robotman2412/PX16/tests/highleveltest.asm

// region text
	// IRQ vector.
	.db irqv
	// NMI vector.
	.db nmiv
	// Entry vector.
	.db entry



	// IRQ Handler.
irqv:
	// Update timer status.
	MOV [PC~timerstatus], 1
	
	// Acknowledge timer.
	MOV [0xfffe], 0x0400
	
	MOV PF, [ST]
	MOV PC, [ST]



	// NMI Handler.
nmiv:
	MOV PF, [ST]
	MOV PC, [ST]



	// Code entrypoint.
entry:
	// Generic initialiser.
	MOV ST, 0xffff
	SUB ST, [0xffff]
	OR  PF, 0x0003
	
	// Show sumthin.
	LEA R1, [PC~img_logo0]
	LEA R2, [PC~img_logo]
.loop:
	MOV R0, R1
	LEA.JSR PC, [PC~disp_img]
	LEA.JSR PC, [PC~waittimer]
	ADD R1, 32
	CMP R1, R2
	LEA.ULE PC, [PC~.loop]
	
	// Ded.
	DEC PC



	// Waits using the timers.
waittimer: // region
	MOV [ST], R0
	
	// Set timer waiting device.
	MOV [PC~timerstatus], 0
	
	// Set timer value.
	MOV R0, 0xffff
	MOV [0xfffa], R0
	MOV [0xfffb], R0
	// Set timer limit.
	MOV [0xfff8], 0xa120
	MOV [0xfff9], 0x0007
	// Start timer.
	MOV [0xfffe], 0x0505
	
	// Enable interrupts.
	OR  PF, 0x0002
	
	// Wait until timerstatus is nonzero.
.loop:
	CMP1 [PC~timerstatus]
	LEA.ULT PC, [PC~.loop]
	
	// Return.
	MOV PC, [ST]
	// endregion



	// Waits for a bit.
waitloop: // region
	MOV [ST], R0
	MOV R0, 0x1000
.loop:
	DEC R0
	LEA.CS PC, [PC~.loop]
	MOV R0, [ST]
	MOV PC, [ST]
	// endregion



	// Simple helper that copies source to the screen.
	// Parameters: src.
disp_img: // region
	// Function entry.
	MOV [ST], R2
	MOV [ST], R1
	
	// Subroutine call: memcpy(0xffc0, src, 32)
	// Set limit to 32 (the size of the screen).
	MOV R2, 32
	// Move over the source to the proper register.
	MOV R1, R0
	// Set dest to 0xffc0 (the address of the screen).
	MOV R0, 0xffc0
	// Jump to subroutine.
	LEA.JSR PC, [PC~memcpy]
	
	// Return.
	MOV R1, [ST]
	MOV R2, [ST]
	MOV PC, [ST]
	// endregion



	// Copies a region of memory to another.
	// Does not check for overlapping memory.
	// Parameters: dst, src, size.
memcpy: // region
	// Function entry.
	MOV [ST], R3
	
	// Limit prep and check size > 0.
	DEC R2
	LEA.ULT PC, [PC~.exit]
	
	// Copying loop.
.loop:
	// Loads from the source.
	MOV R3, [R1+R2]
	// Stores to the destination.
	MOV [R0+R2], R3
	// Decrements the limit.
	DEC R2
	// Loop condition.
	LEA.UGE PC, [PC~.loop]
	
	// Return.
.exit:
	MOV R3, [ST]
	MOV PC, [ST]
	// endregion


//endregion text.



// region rodata
	.section ".rodata"

img_logo0:
	// region
	//    0 ' ' ' ' ' ' ' ' ' ' ' ' ' ' ' ' ' ' ' ' ' ' ' ' ' ' ' ' ' ' 31
	//  0 . . . . . . . . . . . . . . . . . . . . . . . . . . . . . . . .
	//  1 . . . . . . . . . . . . . . . . . . . . . . . . . . . . . . . .
	//  2 . . . . . . . . . . . . . . . . . . . . . . . . . . . . . . . .
	//  3 . . . . . . . . . . . . . . . . . . . . . . . . . . . . . . . .
	//  4 . . . . . . . . . . . . . . . . . . . . . . . . . . . . . . . .
	//  5 . . . . . . . . . . . . . . . . . . . . . . . . . . . . . . . .
	//  6 . . . . . . . . . . . . . . . . . . . . . . . . . . . . . . . .
	//  7 . . . . . . . . . . . . . . . . . . . . . . . . . . . . . . . .
	//  8 . . . . . . . . . . . . . . . . . . . . . . . . . . . . . . . .
	//  9 . . . . . . . . . . . . . . . . . . . . . . . . . . . . . . . .
	// 10 . . . . . . . . . . . . . . . . . . . . . . . . . . . . . . . .
	// 11 . . . . . . . . . . . . . . . . . . . . . . . . . . . . . . . .
	// 12 . @ . . . . . . . . . @ . . . . . . . . . . . . . . . . . . . .
	// 13 . @ . . . . . @ . @ . @ . . . . . @ . @ . . . @ @ . . . . . . .
	// 14 . . . . . . . . . . . . . . . . . . . . . . . . . . . . . . . .
	// 15 . . . . . . . . . . . . . . . . . . . . . . . . . . . . . . . .
	.db 0x0000
	.db 0x3000
	.db 0x0000
	.db 0x0000
	.db 0x0000
	.db 0x0000
	.db 0x0000
	.db 0x2000
	.db 0x0000
	.db 0x2000
	.db 0x0000
	.db 0x3000
	.db 0x0000
	.db 0x0000
	.db 0x0000
	.db 0x0000
	.db 0x0000
	.db 0x2000
	.db 0x0000
	.db 0x2000
	.db 0x0000
	.db 0x0000
	.db 0x0000
	.db 0x2000
	.db 0x2000
	.db 0x0000
	.db 0x0000
	.db 0x0000
	.db 0x0000
	.db 0x0000
	.db 0x0000
	.db 0x0000
	// endregion

img_logo1:
	// region
	//    0 ' ' ' ' ' ' ' ' ' ' ' ' ' ' ' ' ' ' ' ' ' ' ' ' ' ' ' ' ' ' 31
	//  0 . . . . . . . . . . . . . . . . . . . . . . . . . . . . . . . .
	//  1 . . . . . . . . . . . . . . . . . . . . . . . . . . . . . . . .
	//  2 . . . . . . . . . . . . . . . . . . . . . . . . . . . . . . . .
	//  3 . . . . . . . . . . . . . . . . . . . . . . . . . . . . . . . .
	//  4 . . . . . . . . . . . . . . . . . . . . . . . . . . . . . . . .
	//  5 . . . . . . . . . . . . . . . . . . . . . . . . . . . . . . . .
	//  6 . . . . . . . . . . . . . . . . . . . . . . . . . . . . . . . .
	//  7 . . . . . . . . . . . . . . . . . . . . . . . . . . . . . . . .
	//  8 . . . . . . . . . . . . . . . . . . . . . . . . . . . . . . . .
	//  9 . . . . . . . . . . . . . . . . . . . . . . . . . . . . . . . .
	// 10 . @ . . . . . . . . . . . @ . . . . . . . . . . . . . . . . . .
	// 11 . @ . . . . . . . . . . @ . . . . . . . . . . . . . . . . . . .
	// 12 . @ . . . . . . @ . . @ . . . . . . @ . . . . . . . . . . . . .
	// 13 . @ . . . . . @ @ @ . @ . . . . . @ @ @ . @ @ @ @ . . . . . . .
	// 14 . . . . . . . . . . . . . . . . . . . . . . . . . . . . . . . .
	// 15 . . . . . . . . . . . . . . . . . . . . . . . . . . . . . . . .
	.db 0x0000
	.db 0x3c00
	.db 0x0000
	.db 0x0000
	.db 0x0000
	.db 0x0000
	.db 0x0000
	.db 0x2000
	.db 0x3000
	.db 0x2000
	.db 0x0000
	.db 0x3000
	.db 0x0800
	.db 0x0400
	.db 0x0000
	.db 0x0000
	.db 0x0000
	.db 0x2000
	.db 0x3000
	.db 0x2000
	.db 0x0000
	.db 0x2000
	.db 0x2000
	.db 0x2000
	.db 0x2000
	.db 0x0000
	.db 0x0000
	.db 0x0000
	.db 0x0000
	.db 0x0000
	.db 0x0000
	.db 0x0000
	// endregion

img_logo2:
	// region
	//    0 ' ' ' ' ' ' ' ' ' ' ' ' ' ' ' ' ' ' ' ' ' ' ' ' ' ' ' ' ' ' 31
	//  0 . . . . . . . . . . . . . . . . . . . . . . . . . . . . . . . .
	//  1 . . . . . . . . . . . . . . . . . . . . . . . . . . . . . . . .
	//  2 . . . . . . . . . . . . . . . . . . . . . . . . . . . . . . . .
	//  3 . . . . . . . . . . . . . . . . . . . . . . . . . . . . . . . .
	//  4 . . . . . . . . . . . . . . . . . . . . . . . . . . . . . . . .
	//  5 . . . . . . . . . . . . . . . . . . . . . . . . . . . . . . . .
	//  6 . . . . . . . . . . . . . . . . . . . . . . . . . . . . . . . .
	//  7 . . . . . . . . . . . . . . . . . . . . . . . . . . . . . . . .
	//  8 . @ . . . . . . . . . . . . . . . . . . . . . . . . . . . . . .
	//  9 . @ . . . . . . . . . . @ . @ . . . . . . . . . . . . . . . . .
	// 10 . @ . . . . . . @ . . . . @ . . . . @ . . . . . . . . . . . . .
	// 11 . @ . . . . . . @ . . . @ . @ . . . @ . . @ . . . . . . . . . .
	// 12 . @ . . . . . . @ . . @ . . . . . . @ . . @ . . . . . . . . . .
	// 13 . @ . . . . . @ @ @ . @ . . . . . @ @ @ . @ @ @ @ . . . . . . .
	// 14 . . . . . . . . . . . . . . . . . . . . . . . . . . . . . . . .
	// 15 . . . . . . . . . . . . . . . . . . . . . . . . . . . . . . . .
	.db 0x0000
	.db 0x3f00
	.db 0x0000
	.db 0x0000
	.db 0x0000
	.db 0x0000
	.db 0x0000
	.db 0x2000
	.db 0x3c00
	.db 0x2000
	.db 0x0000
	.db 0x3000
	.db 0x0a00
	.db 0x0400
	.db 0x0a00
	.db 0x0000
	.db 0x0000
	.db 0x2000
	.db 0x3c00
	.db 0x2000
	.db 0x0000
	.db 0x3800
	.db 0x2000
	.db 0x2000
	.db 0x2000
	.db 0x0000
	.db 0x0000
	.db 0x0000
	.db 0x0000
	.db 0x0000
	.db 0x0000
	.db 0x0000
	// endregion

img_logo3:
	// region
	//    0 ' ' ' ' ' ' ' ' ' ' ' ' ' ' ' ' ' ' ' ' ' ' ' ' ' ' ' ' ' ' 31
	//  0 . . . . . . . . . . . . . . . . . . . . . . . . . . . . . . . .
	//  1 . . . . . . . . . . . . . . . . . . . . . . . . . . . . . . . .
	//  2 . . . . . . . . . . . . . . . . . . . . . . . . . . . . . . . .
	//  3 . . . . . . . . . . . . . . . . . . . . . . . . . . . . . . . .
	//  4 . . . . . . . . . . . . . . . . . . . . . . . . . . . . . . . .
	//  5 . . . . . . . . . . . . . . . . . . . . . . . . . . . . . . . .
	//  6 . @ . . . . . . . . . . . . . . . . . . . . . . . . . . . . . .
	//  7 . @ . . . . . . . . . . . . . . . . . . . . . . . . . . . . . .
	//  8 . @ . . . . . . @ . . @ . . . @ . . @ . . . . . . . . . . . . .
	//  9 . @ . . . . . . @ . . . @ . @ . . . @ . . . . . . . . . . . . .
	// 10 . @ . . . . . . @ . . . . @ . . . . @ . . @ @ . . . . . . . . .
	// 11 . @ . . . . . . @ . . . @ . @ . . . @ . . @ . . . . . . . . . .
	// 12 . @ . . . . . . @ . . @ . . . @ . . @ . . @ . . . . . . . . . .
	// 13 . @ . . . . . @ @ @ . @ . . . . . @ @ @ . @ @ @ @ . . . . . . .
	// 14 . . . . . . . . . . . . . . . . . . . . . . . . . . . . . . . .
	// 15 . . . . . . . . . . . . . . . . . . . . . . . . . . . . . . . .
	.db 0x0000
	.db 0x3fc0
	.db 0x0000
	.db 0x0000
	.db 0x0000
	.db 0x0000
	.db 0x0000
	.db 0x2000
	.db 0x3f00
	.db 0x2000
	.db 0x0000
	.db 0x3100
	.db 0x0a00
	.db 0x0400
	.db 0x0a00
	.db 0x1100
	.db 0x0000
	.db 0x2000
	.db 0x3f00
	.db 0x2000
	.db 0x0000
	.db 0x3c00
	.db 0x2400
	.db 0x2000
	.db 0x2000
	.db 0x0000
	.db 0x0000
	.db 0x0000
	.db 0x0000
	.db 0x0000
	.db 0x0000
	.db 0x0000
	// endregion

img_logo4:
	// region
	//    0 ' ' ' ' ' ' ' ' ' ' ' ' ' ' ' ' ' ' ' ' ' ' ' ' ' ' ' ' ' ' 31
	//  0 . . . . . . . . . . . . . . . . . . . . . . . . . . . . . . . .
	//  1 . . . . . . . . . . . . . . . . . . . . . . . . . . . . . . . .
	//  2 . . . . . . . . . . . . . . . . . . . . . . . . . . . . . . . .
	//  3 . . . . . . . . . . . . . . . . . . . . . . . . . . . . . . . .
	//  4 . @ . . . . . . . . . . . . . . . . . . . . . . . . . . . . . .
	//  5 . @ . . . . . . . . . . . . . . . . . . . . . . . . . . . . . .
	//  6 . @ . . . . . . . . . . . . . . . . . . . . . . . . . . . . . .
	//  7 . @ . . . . . @ @ . . @ . . . @ . @ @ . . . . . . . . . . . . .
	//  8 . @ . . . . . . @ . . @ . . . @ . . @ . . @ . . . . . . . . . .
	//  9 . @ . . . . . . @ . . . @ . @ . . . @ . . @ . . . . . . . . . .
	// 10 . @ . . . . . . @ . . . . @ . . . . @ . . @ @ @ . . . . . . . .
	// 11 . @ . . . . . . @ . . . @ . @ . . . @ . . @ . . . . . . . . . .
	// 12 . @ . . . . . . @ . . @ . . . @ . . @ . . @ . . . . . . . . . .
	// 13 . @ . . . . . @ @ @ . @ . . . @ . @ @ @ . @ @ @ @ . . . . . . .
	// 14 . . . . . . . . . . . . . . . . . . . . . . . . . . . . . . . .
	// 15 . . . . . . . . . . . . . . . . . . . . . . . . . . . . . . . .
	.db 0x0000
	.db 0x3ff0
	.db 0x0000
	.db 0x0000
	.db 0x0000
	.db 0x0000
	.db 0x0000
	.db 0x2080
	.db 0x3f80
	.db 0x2000
	.db 0x0000
	.db 0x3180
	.db 0x0a00
	.db 0x0400
	.db 0x0a00
	.db 0x3180
	.db 0x0000
	.db 0x2080
	.db 0x3f80
	.db 0x2000
	.db 0x0000
	.db 0x3f00
	.db 0x2400
	.db 0x2400
	.db 0x2000
	.db 0x0000
	.db 0x0000
	.db 0x0000
	.db 0x0000
	.db 0x0000
	.db 0x0000
	.db 0x0000
	// endregion

img_logo5:
	// region
	//    0 ' ' ' ' ' ' ' ' ' ' ' ' ' ' ' ' ' ' ' ' ' ' ' ' ' ' ' ' ' ' 31
	//  0 . . . . . . . . . . . . . . . . . . . . . . . . . . . . . . . .
	//  1 . . . . . . . . . . . . . . . . . . . . . . . . . . . . . . . .
	//  2 . @ . . . . . . . . . . . . . . . . . . . . . . . . . . . . . .
	//  3 . @ . . . . . . . . . . . . . . . . . . . . . . . . . . . . . .
	//  4 . @ . . . . . . . . . . . . . . . . . . . . . . . . . . . . . .
	//  5 . @ . . . . . . . . . . . . . . . . . . . . . . . . . . . . . .
	//  6 . @ . . . . . . . . . . . . . . . . . . . . . . . . . . . . . .
	//  7 . @ . . . . . @ @ . . @ . . . @ . @ @ . . @ @ . . . . . . . . .
	//  8 . @ . . . . . . @ . . @ . . . @ . . @ . . @ . . . . . . . . . .
	//  9 . @ . . . . . . @ . . . @ . @ . . . @ . . @ . . . . . . . . . .
	// 10 . @ . . . . . . @ . . . . @ . . . . @ . . @ @ @ . . . . . . . .
	// 11 . @ . . . . . . @ . . . @ . @ . . . @ . . @ . . . . . . . . . .
	// 12 . @ . . . . . . @ . . @ . . . @ . . @ . . @ . . . . . . . . . .
	// 13 . @ . . . . . @ @ @ . @ . . . @ . @ @ @ . @ @ @ @ . . . . . . .
	// 14 . . . . . . . . . . . . . . . . . . . . . . . . . . . . . . . .
	// 15 . . . . . . . . . . . . . . . . . . . . . . . . . . . . . . . .
	.db 0x0000
	.db 0x3ffc
	.db 0x0000
	.db 0x0000
	.db 0x0000
	.db 0x0000
	.db 0x0000
	.db 0x2080
	.db 0x3f80
	.db 0x2000
	.db 0x0000
	.db 0x3180
	.db 0x0a00
	.db 0x0400
	.db 0x0a00
	.db 0x3180
	.db 0x0000
	.db 0x2080
	.db 0x3f80
	.db 0x2000
	.db 0x0000
	.db 0x3f80
	.db 0x2480
	.db 0x2400
	.db 0x2000
	.db 0x0000
	.db 0x0000
	.db 0x0000
	.db 0x0000
	.db 0x0000
	.db 0x0000
	.db 0x0000
	// endregion

img_logo6:
	// region
	//    0 ' ' ' ' ' ' ' ' ' ' ' ' ' ' ' ' ' ' ' ' ' ' ' ' ' ' ' ' ' ' 31
	//  0 . . . . . . . . . . . . . . . . . . . . . . . . . . . . . . . .
	//  1 . . . . . . . . . . . . . . . . . . . . . . . . . . . . . . . .
	//  2 . @ @ @ . . . . . . . . . . . . . . . . . . . . . . . . . . . .
	//  3 . @ . . . . . . . . . . . . . . . . . . . . . . . . . . . . . .
	//  4 . @ . . . . . . . . . . . . . . . . . . . . . . . . . . . . . .
	//  5 . @ . . . . . . . . . . . . . . . . . . . . . . . . . . . . . .
	//  6 . @ . . . . . . . . . . . . . . . . . . . . . . . . . . . . . .
	//  7 . @ . . . . . @ @ . . @ . . . @ . @ @ . . @ @ @ @ . . . . . . .
	//  8 . @ . . . . . . @ . . @ . . . @ . . @ . . @ . . . . . . . . . .
	//  9 . @ . . . . . . @ . . . @ . @ . . . @ . . @ . . . . . . . . . .
	// 10 . @ . . . . . . @ . . . . @ . . . . @ . . @ @ @ . . . . . . . .
	// 11 . @ . . . . . . @ . . . @ . @ . . . @ . . @ . . . . . . . . . .
	// 12 . @ . . . . . . @ . . @ . . . @ . . @ . . @ . . . . . . . . . .
	// 13 . @ . . . . . @ @ @ . @ . . . @ . @ @ @ . @ @ @ @ . . . . . . .
	// 14 . . . . . . . . . . . . . . . . . . . . . . . . . . . . . . . .
	// 15 . . . . . . . . . . . . . . . . . . . . . . . . . . . . . . . .
	.db 0x0000
	.db 0x3ffc
	.db 0x0004
	.db 0x0004
	.db 0x0000
	.db 0x0000
	.db 0x0000
	.db 0x2080
	.db 0x3f80
	.db 0x2000
	.db 0x0000
	.db 0x3180
	.db 0x0a00
	.db 0x0400
	.db 0x0a00
	.db 0x3180
	.db 0x0000
	.db 0x2080
	.db 0x3f80
	.db 0x2000
	.db 0x0000
	.db 0x3f80
	.db 0x2480
	.db 0x2480
	.db 0x2080
	.db 0x0000
	.db 0x0000
	.db 0x0000
	.db 0x0000
	.db 0x0000
	.db 0x0000
	.db 0x0000
	// endregion

img_logo7:
	// region
	//    0 ' ' ' ' ' ' ' ' ' ' ' ' ' ' ' ' ' ' ' ' ' ' ' ' ' ' ' ' ' ' 31
	//  0 . . . . . . . . . . . . . . . . . . . . . . . . . . . . . . . .
	//  1 . . . . . . . . . . . . . . . . . . . . . . . . . . . . . . . .
	//  2 . @ @ @ . . . . . . . . . . . . . . . . . . . . . . . . . . . .
	//  3 . @ . . @ . . . . . . . . . . . . . . . . . . . . . . . . . . .
	//  4 . @ . . . @ . . . . . . . . . . . . . . . . . . . . . . . . . .
	//  5 . @ . . . . . . . . . . . . . . . . . . . . . . . . . . . . . .
	//  6 . @ . . . . . . . . . . . . . . . . . . . . . . . . . . . . . .
	//  7 . @ . . . . . @ @ . . @ . . . @ . @ @ . . @ @ @ @ . . . . . . .
	//  8 . @ . . . . . . @ . . @ . . . @ . . @ . . @ . . . . . . . . . .
	//  9 . @ . . . . . . @ . . . @ . @ . . . @ . . @ . . . . . . . . . .
	// 10 . @ . . . . . . @ . . . . @ . . . . @ . . @ @ @ . . . . . . . .
	// 11 . @ . . . . . . @ . . . @ . @ . . . @ . . @ . . . . . . . . . .
	// 12 . @ . . . . . . @ . . @ . . . @ . . @ . . @ . . . . . . . . . .
	// 13 . @ . . . . . @ @ @ . @ . . . @ . @ @ @ . @ @ @ @ . . . . . . .
	// 14 . . . . . . . . . . . . . . . . . . . . . . . . . . . . . . . .
	// 15 . . . . . . . . . . . . . . . . . . . . . . . . . . . . . . . .
	.db 0x0000
	.db 0x3ffc
	.db 0x0004
	.db 0x0004
	.db 0x0008
	.db 0x0010
	.db 0x0000
	.db 0x2080
	.db 0x3f80
	.db 0x2000
	.db 0x0000
	.db 0x3180
	.db 0x0a00
	.db 0x0400
	.db 0x0a00
	.db 0x3180
	.db 0x0000
	.db 0x2080
	.db 0x3f80
	.db 0x2000
	.db 0x0000
	.db 0x3f80
	.db 0x2480
	.db 0x2480
	.db 0x2080
	.db 0x0000
	.db 0x0000
	.db 0x0000
	.db 0x0000
	.db 0x0000
	.db 0x0000
	.db 0x0000
	// endregion

img_logo8:
	// region
	//    0 ' ' ' ' ' ' ' ' ' ' ' ' ' ' ' ' ' ' ' ' ' ' ' ' ' ' ' ' ' ' 31
	//  0 . . . . . . . . . . . . . . . . . . . . . . . . . . . . . . . .
	//  1 . . . . . . . . . . . . . . . . . . . . . . . . . . . . . . . .
	//  2 . @ @ @ . . . . . . . . . . . . . . . . . . . . . . . . . . . .
	//  3 . @ . . @ . . . . . . . . . . . . . . . . . . . . . . . . . . .
	//  4 . @ . . . @ . . . . . . . . . . . . . . . . . . . . . . . . . .
	//  5 . @ . . . @ . . . . . . . . . . . . . . . . . . . . . . . . . .
	//  6 . @ . . @ . . . . . . . . . . . . . . . . . . . . . . . . . . .
	//  7 . @ . . . . . @ @ . . @ . . . @ . @ @ . . @ @ @ @ . . . . . . .
	//  8 . @ . . . . . . @ . . @ . . . @ . . @ . . @ . . . . . . . . . .
	//  9 . @ . . . . . . @ . . . @ . @ . . . @ . . @ . . . . . . . . . .
	// 10 . @ . . . . . . @ . . . . @ . . . . @ . . @ @ @ . . . . . . . .
	// 11 . @ . . . . . . @ . . . @ . @ . . . @ . . @ . . . . . . . . . .
	// 12 . @ . . . . . . @ . . @ . . . @ . . @ . . @ . . . . . . . . . .
	// 13 . @ . . . . . @ @ @ . @ . . . @ . @ @ @ . @ @ @ @ . . . . . . .
	// 14 . . . . . . . . . . . . . . . . . . . . . . . . . . . . . . . .
	// 15 . . . . . . . . . . . . . . . . . . . . . . . . . . . . . . . .
	.db 0x0000
	.db 0x3ffc
	.db 0x0004
	.db 0x0004
	.db 0x0048
	.db 0x0030
	.db 0x0000
	.db 0x2080
	.db 0x3f80
	.db 0x2000
	.db 0x0000
	.db 0x3180
	.db 0x0a00
	.db 0x0400
	.db 0x0a00
	.db 0x3180
	.db 0x0000
	.db 0x2080
	.db 0x3f80
	.db 0x2000
	.db 0x0000
	.db 0x3f80
	.db 0x2480
	.db 0x2480
	.db 0x2080
	.db 0x0000
	.db 0x0000
	.db 0x0000
	.db 0x0000
	.db 0x0000
	.db 0x0000
	.db 0x0000
	// endregion

img_logo9:
	// region
	//    0 ' ' ' ' ' ' ' ' ' ' ' ' ' ' ' ' ' ' ' ' ' ' ' ' ' ' ' ' ' ' 31
	//  0 . . . . . . . . . . . . . . . . . . . . . . . . . . . . . . . .
	//  1 . . . . . . . . . . . . . . . . . . . . . . . . . . . . . . . .
	//  2 . @ @ @ . . . . . . . . . . . . . . . . . . . . . . . . . . . .
	//  3 . @ . . @ . . . . . . . . . . . . . . . . . . . . . . . . . . .
	//  4 . @ . . . @ . . . . . . . . . . . . . . . . . . . . . . . . . .
	//  5 . @ . . . @ . . . . . . . . . . . . . . . . . . . . . . . . . .
	//  6 . @ . . @ . . . . . . . . . . . . . . . . . . . . . . . . . . .
	//  7 . @ . @ . . . @ @ . . @ . . . @ . @ @ . . @ @ @ @ . . . . . . .
	//  8 . @ . . . . . . @ . . @ . . . @ . . @ . . @ . . . . . . . . . .
	//  9 . @ . . . . . . @ . . . @ . @ . . . @ . . @ . . . . . . . . . .
	// 10 . @ . . . . . . @ . . . . @ . . . . @ . . @ @ @ . . . . . . . .
	// 11 . @ . . . . . . @ . . . @ . @ . . . @ . . @ . . . . . . . . . .
	// 12 . @ . . . . . . @ . . @ . . . @ . . @ . . @ . . . . . . . . . .
	// 13 . @ . . . . . @ @ @ . @ . . . @ . @ @ @ . @ @ @ @ . . . . . . .
	// 14 . . . . . . . . . . . . . . . . . . . . . . . . . . . . . . . .
	// 15 . . . . . . . . . . . . . . . . . . . . . . . . . . . . . . . .
	.db 0x0000
	.db 0x3ffc
	.db 0x0004
	.db 0x0084
	.db 0x0048
	.db 0x0030
	.db 0x0000
	.db 0x2080
	.db 0x3f80
	.db 0x2000
	.db 0x0000
	.db 0x3180
	.db 0x0a00
	.db 0x0400
	.db 0x0a00
	.db 0x3180
	.db 0x0000
	.db 0x2080
	.db 0x3f80
	.db 0x2000
	.db 0x0000
	.db 0x3f80
	.db 0x2480
	.db 0x2480
	.db 0x2080
	.db 0x0000
	.db 0x0000
	.db 0x0000
	.db 0x0000
	.db 0x0000
	.db 0x0000
	.db 0x0000
	// endregion

img_logo10:
	// region
	//    0 ' ' ' ' ' ' ' ' ' ' ' ' ' ' ' ' ' ' ' ' ' ' ' ' ' ' ' ' ' ' 31
	//  0 . . . . . . . . . . . . . . . . . . . . . . . . . . . . . . . .
	//  1 . . . . . . . . . . . . . . . . . . . . . . . . . . . . . . . .
	//  2 . @ @ @ . . . . . . . . . . . . . . . . . . . . . . . . . . . .
	//  3 . @ . . @ . . . . . . . . . . . . . . . . . . . . . . . . . . .
	//  4 . @ . . . @ . . . . . . . . . . . . . . . . . . . . . . . . . .
	//  5 . @ . . . @ . . @ . . . . . . . . . . . . . . . . . . . . . . .
	//  6 . @ . . @ . . . . . . . . . . . . . . . . . . . . . . . . . . .
	//  7 . @ . @ . . . @ @ . . @ . . . @ . @ @ . . @ @ @ @ . . . . . . .
	//  8 . @ . . . . . . @ . . @ . . . @ . . @ . . @ . . . . . . . . . .
	//  9 . @ . . . . . . @ . . . @ . @ . . . @ . . @ . . . . . . . . . .
	// 10 . @ . . . . . . @ . . . . @ . . . . @ . . @ @ @ . . . . . . . .
	// 11 . @ . . . . . . @ . . . @ . @ . . . @ . . @ . . . . . . . . . .
	// 12 . @ . . . . . . @ . . @ . . . @ . . @ . . @ . . . . . . . . . .
	// 13 . @ . . . . . @ @ @ . @ . . . @ . @ @ @ . @ @ @ @ . . . . . . .
	// 14 . . . . . . . . . . . . . . . . . . . . . . . . . . . . . . . .
	// 15 . . . . . . . . . . . . . . . . . . . . . . . . . . . . . . . .
	.db 0x0000
	.db 0x3ffc
	.db 0x0004
	.db 0x0084
	.db 0x0048
	.db 0x0030
	.db 0x0000
	.db 0x2080
	.db 0x3fa0
	.db 0x2000
	.db 0x0000
	.db 0x3180
	.db 0x0a00
	.db 0x0400
	.db 0x0a00
	.db 0x3180
	.db 0x0000
	.db 0x2080
	.db 0x3f80
	.db 0x2000
	.db 0x0000
	.db 0x3f80
	.db 0x2480
	.db 0x2480
	.db 0x2080
	.db 0x0000
	.db 0x0000
	.db 0x0000
	.db 0x0000
	.db 0x0000
	.db 0x0000
	.db 0x0000
	// endregion

img_logo11:
	// region
	//    0 ' ' ' ' ' ' ' ' ' ' ' ' ' ' ' ' ' ' ' ' ' ' ' ' ' ' ' ' ' ' 31
	//  0 . . . . . . . . . . . . . . . . . . . . . . . . . . . . . . . .
	//  1 . . . . . . . . . . . . . . . . . . . . . . . . . . . . . . . .
	//  2 . @ @ @ . . . . . . . . . . . . . . . . . . . . . . . . . . . .
	//  3 . @ . . @ . . . . . . . . . . . . . . . . . . . . . . . . . . .
	//  4 . @ . . . @ . . . . . . . . . . . . . . . . . . . . . . . . . .
	//  5 . @ . . . @ . . @ . . . . . . . . . @ . . . . . . . . . . . . .
	//  6 . @ . . @ . . . . . . . . . . . . . . . . . . . . . . . . . . .
	//  7 . @ . @ . . . @ @ . . @ . . . @ . @ @ . . @ @ @ @ . . . . . . .
	//  8 . @ . . . . . . @ . . @ . . . @ . . @ . . @ . . . . . . . . . .
	//  9 . @ . . . . . . @ . . . @ . @ . . . @ . . @ . . . . . . . . . .
	// 10 . @ . . . . . . @ . . . . @ . . . . @ . . @ @ @ . . . . . . . .
	// 11 . @ . . . . . . @ . . . @ . @ . . . @ . . @ . . . . . . . . . .
	// 12 . @ . . . . . . @ . . @ . . . @ . . @ . . @ . . . . . . . . . .
	// 13 . @ . . . . . @ @ @ . @ . . . @ . @ @ @ . @ @ @ @ . . . . . . .
	// 14 . . . . . . . . . . . . . . . . . . . . . . . . . . . . . . . .
	// 15 . . . . . . . . . . . . . . . . . . . . . . . . . . . . . . . .
	.db 0x0000
	.db 0x3ffc
	.db 0x0004
	.db 0x0084
	.db 0x0048
	.db 0x0030
	.db 0x0000
	.db 0x2080
	.db 0x3fa0
	.db 0x2000
	.db 0x0000
	.db 0x3180
	.db 0x0a00
	.db 0x0400
	.db 0x0a00
	.db 0x3180
	.db 0x0000
	.db 0x2080
	.db 0x3fa0
	.db 0x2000
	.db 0x0000
	.db 0x3f80
	.db 0x2480
	.db 0x2480
	.db 0x2080
	.db 0x0000
	.db 0x0000
	.db 0x0000
	.db 0x0000
	.db 0x0000
	.db 0x0000
	.db 0x0000
	// endregion

img_logo12:
	// region
	//    0 ' ' ' ' ' ' ' ' ' ' ' ' ' ' ' ' ' ' ' ' ' ' ' ' ' ' ' ' ' ' 31
	//  0 . . . . . . . . . . . . . . . . . . . . . . . . . . . . . . . .
	//  1 . . . . . . . . . . . . . . . . . . . . . . . . . . . . . . . .
	//  2 . @ @ @ . . . . . . . . . . . . . . . . . . . . . . @ . . . . .
	//  3 . @ . . @ . . . . . . . . . . . . . . . . . . . . . @ . . . . .
	//  4 . @ . . . @ . . . . . . . . . . . . . . . . . . . . @ . . . . .
	//  5 . @ . . . @ . . @ . . . . . . . . . @ . . . . . . . @ . . . . .
	//  6 . @ . . @ . . . . . . . . . . . . . . . . . . . . . @ . . . . .
	//  7 . @ . @ . . . @ @ . . @ . . . @ . @ @ . . @ @ @ @ . . . . . . .
	//  8 . @ . . . . . . @ . . @ . . . @ . . @ . . @ . . . . . . . . . .
	//  9 . @ . . . . . . @ . . . @ . @ . . . @ . . @ . . . . . . . . . .
	// 10 . @ . . . . . . @ . . . . @ . . . . @ . . @ @ @ . . . . . . . .
	// 11 . @ . . . . . . @ . . . @ . @ . . . @ . . @ . . . . . . . . . .
	// 12 . @ . . . . . . @ . . @ . . . @ . . @ . . @ . . . . . . . . . .
	// 13 . @ . . . . . @ @ @ . @ . . . @ . @ @ @ . @ @ @ @ . . . . . . .
	// 14 . . . . . . . . . . . . . . . . . . . . . . . . . . . . . . . .
	// 15 . . . . . . . . . . . . . . . . . . . . . . . . . . . . . . . .
	.db 0x0000
	.db 0x3ffc
	.db 0x0004
	.db 0x0084
	.db 0x0048
	.db 0x0030
	.db 0x0000
	.db 0x2080
	.db 0x3fa0
	.db 0x2000
	.db 0x0000
	.db 0x3180
	.db 0x0a00
	.db 0x0400
	.db 0x0a00
	.db 0x3180
	.db 0x0000
	.db 0x2080
	.db 0x3fa0
	.db 0x2000
	.db 0x0000
	.db 0x3f80
	.db 0x2480
	.db 0x2480
	.db 0x2080
	.db 0x0000
	.db 0x007c
	.db 0x0000
	.db 0x0000
	.db 0x0000
	.db 0x0000
	.db 0x0000
	// endregion

img_logo:
	// region
	//    0 ' ' ' ' ' ' ' ' ' ' ' ' ' ' ' ' ' ' ' ' ' ' ' ' ' ' ' ' ' ' 31
	//  0 . . . . . . . . . . . . . . . . . . . . . . . . . . . . . . . .
	//  1 . . . . . . . . . . . . . . . . . . . . . . . . . . . . . . . .
	//  2 . @ @ @ . . . . . . . . . . . . . . . . . . . . . . @ . @ @ @ .
	//  3 . @ . . @ . . . . . . . . . . . . . . . . . . . . . @ . @ . . .
	//  4 . @ . . . @ . . . . . . . . . . . . . . . . . . . . @ . @ @ @ .
	//  5 . @ . . . @ . . @ . . . . . . . . . @ . . . . . . . @ . @ . @ .
	//  6 . @ . . @ . . . . . . . . . . . . . . . . . . . . . @ . @ @ @ .
	//  7 . @ . @ . . . @ @ . . @ . . . @ . @ @ . . @ @ @ @ . . . . . . .
	//  8 . @ . . . . . . @ . . @ . . . @ . . @ . . @ . . . . . . . . . .
	//  9 . @ . . . . . . @ . . . @ . @ . . . @ . . @ . . . . . . . . . .
	// 10 . @ . . . . . . @ . . . . @ . . . . @ . . @ @ @ . . . . . . . .
	// 11 . @ . . . . . . @ . . . @ . @ . . . @ . . @ . . . . . . . . . .
	// 12 . @ . . . . . . @ . . @ . . . @ . . @ . . @ . . . . . . . . . .
	// 13 . @ . . . . . @ @ @ . @ . . . @ . @ @ @ . @ @ @ @ . . . . . . .
	// 14 . . . . . . . . . . . . . . . . . . . . . . . . . . . . . . . .
	// 15 . . . . . . . . . . . . . . . . . . . . . . . . . . . . . . . .
	.db 0x0000
	.db 0x3ffc
	.db 0x0004
	.db 0x0084
	.db 0x0048
	.db 0x0030
	.db 0x0000
	.db 0x2080
	.db 0x3fa0
	.db 0x2000
	.db 0x0000
	.db 0x3180
	.db 0x0a00
	.db 0x0400
	.db 0x0a00
	.db 0x3180
	.db 0x0000
	.db 0x2080
	.db 0x3fa0
	.db 0x2000
	.db 0x0000
	.db 0x3f80
	.db 0x2480
	.db 0x2480
	.db 0x2080
	.db 0x0000
	.db 0x007c
	.db 0x0000
	.db 0x007c
	.db 0x0054
	.db 0x0074
	.db 0x0000
	// endregion

// endregion rodata



// region bss
	.section ".bss"
timerstatus:
	.zero 1
// endregion bss
